rusefi/hw_microRusEfi/gerbers/0.4.8/placement_0.4.8.corrected.png

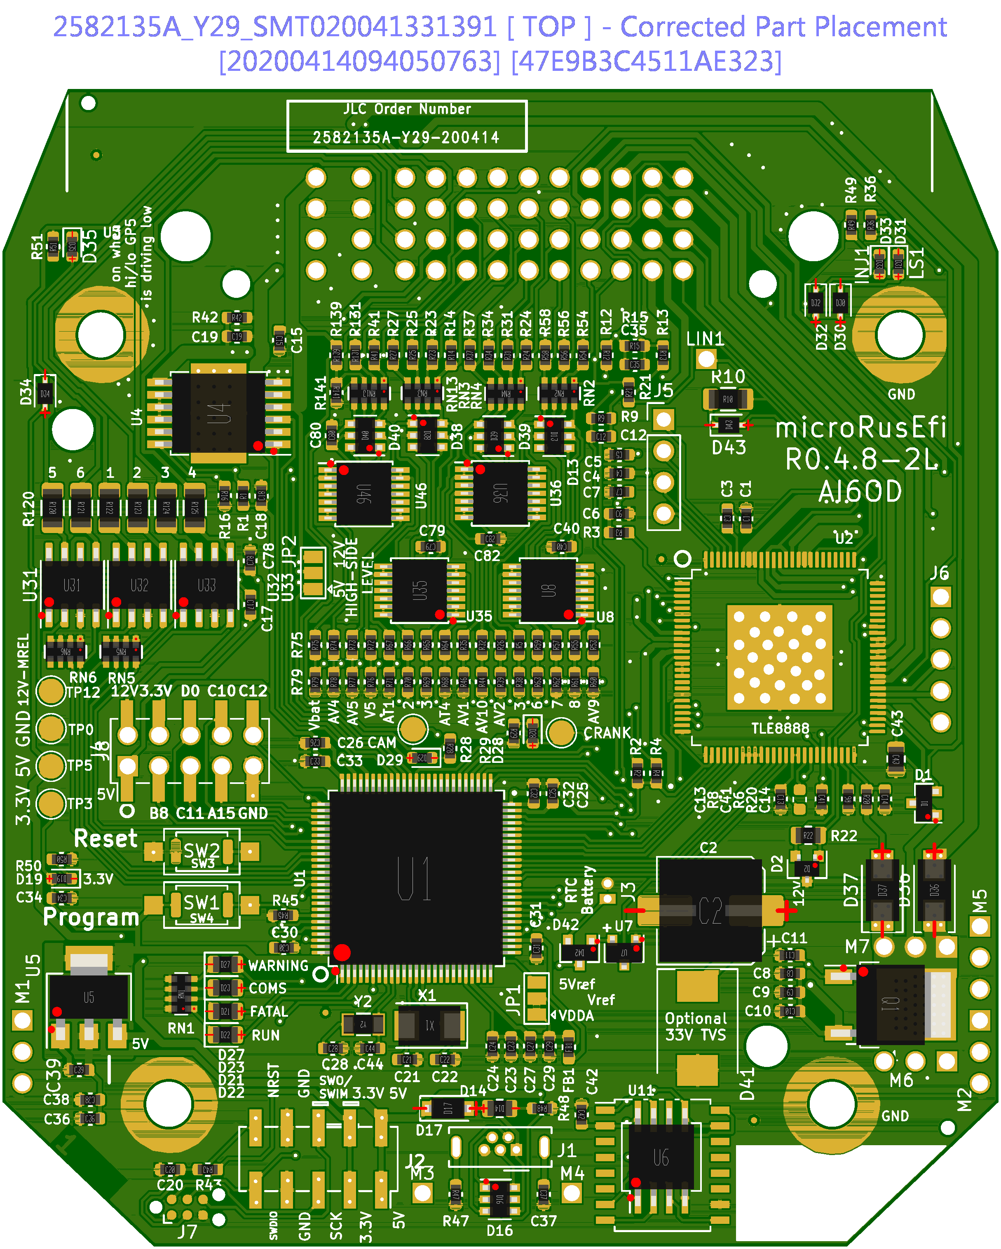
gerbers/0.4.8/placement_0.4.8.corrected.png
