rusefi/hw_microRusEfi/gerbers/0.4.8/placement_0.4.8.corrections.png

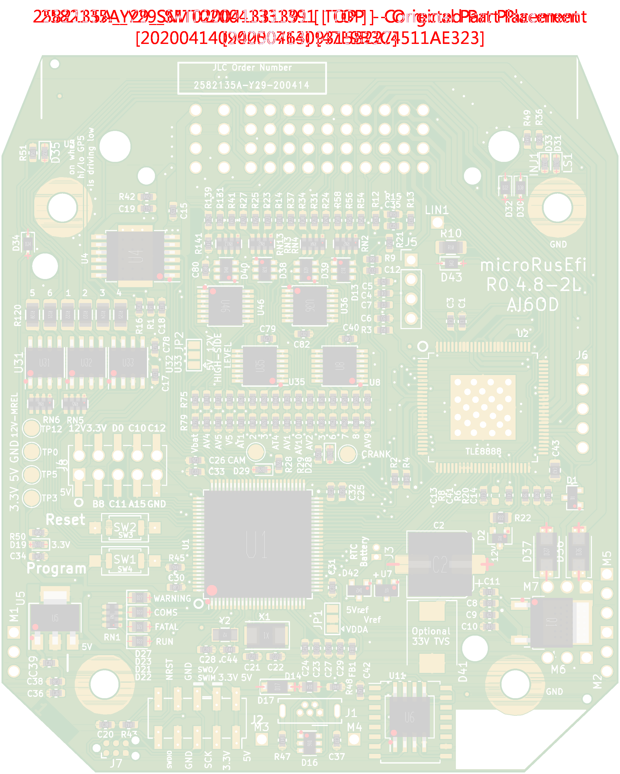
gerbers/0.4.8/placement_0.4.8.corrections.png
