rusefi/hw_microRusEfi/gerbers/0.5.0/placement_0.5.0.corrections.png

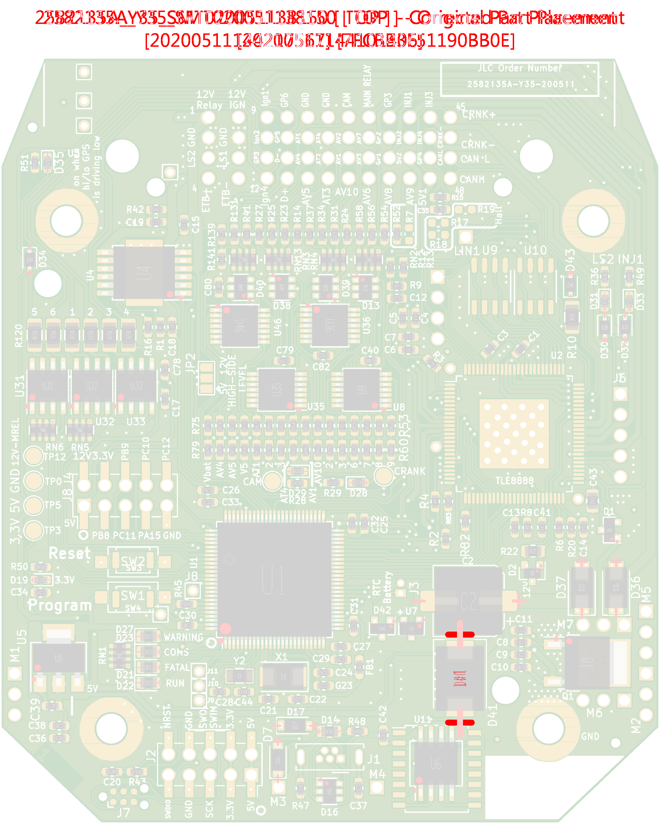
gerbers/0.5.0/placement_0.5.0.corrections.png
