rusefi/hw_microRusEfi/gerbers/R0.5.2/placement_0.5.2.corrected.png

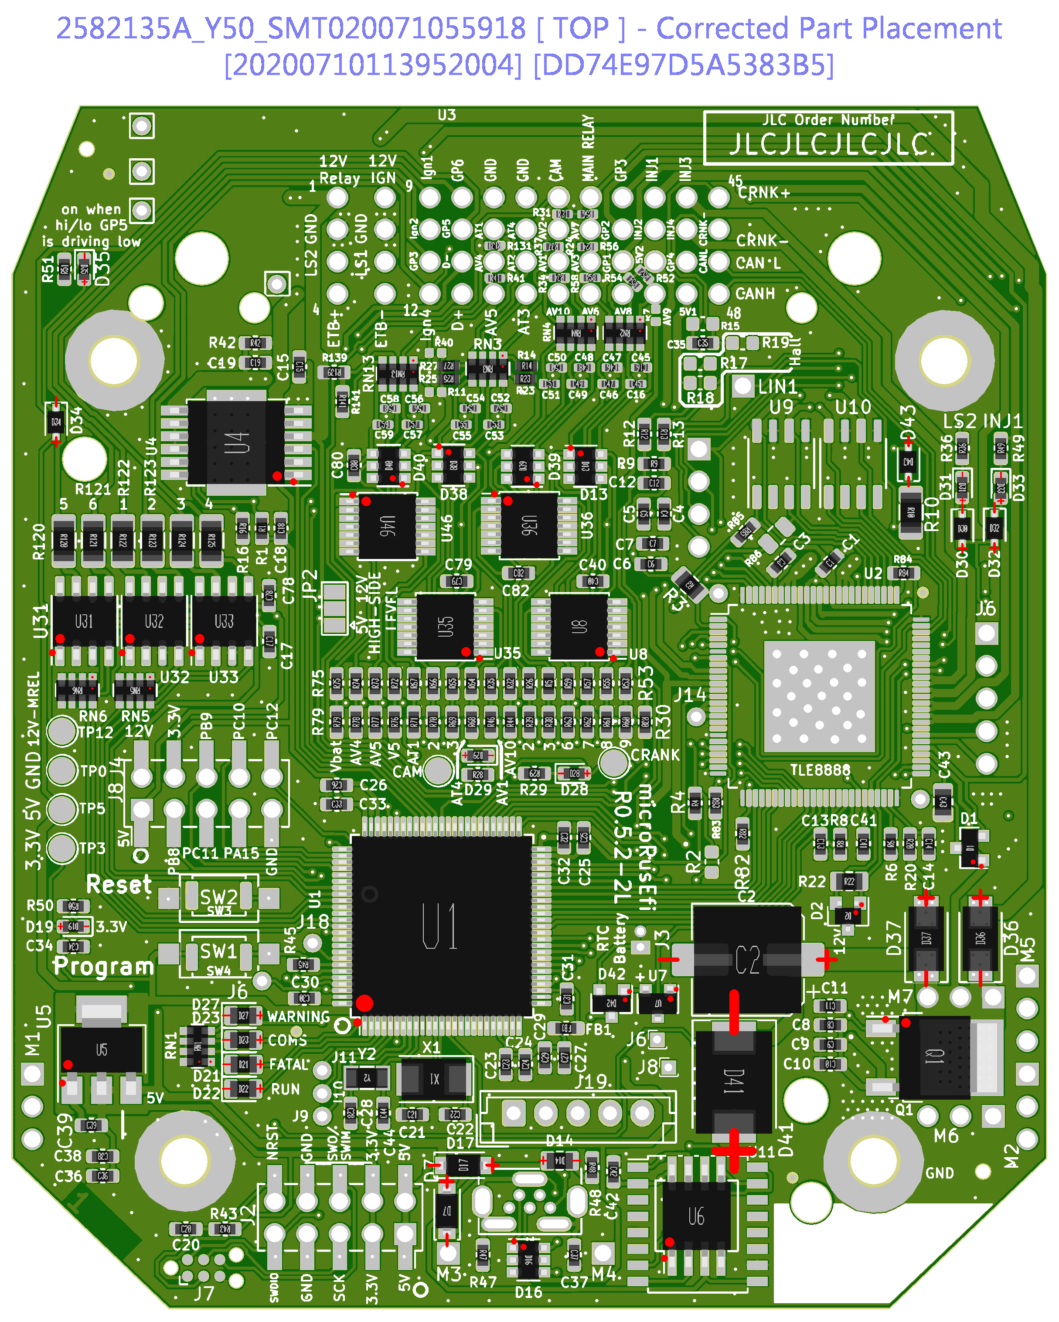
gerbers/R0.5.2/placement_0.5.2.corrected.png
