rusefi/hw_microRusEfi/gerbers/R0.6.0/92-Produce_DanZhi.SMT_Original_Snapshot.Bottom.2582135A_Y484.SMT024101961142.png

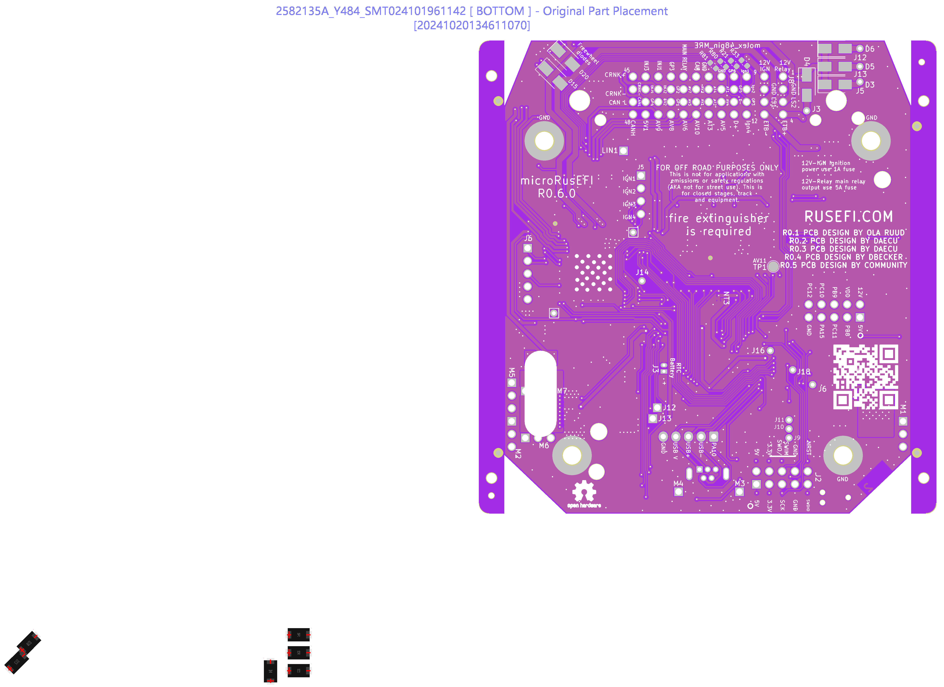
gerbers/R0.6.0/92-Produce_DanZhi.SMT_Original_Snapshot.Bottom.2582135A_Y484.SMT024101961142.png
