rusefi/hw_microRusEfi/gerbers/R0.6.0/31968-Produce_DanZhi.SMT_Original_Snapshot.Top.2582135A_Y484.SMT024101961142.png

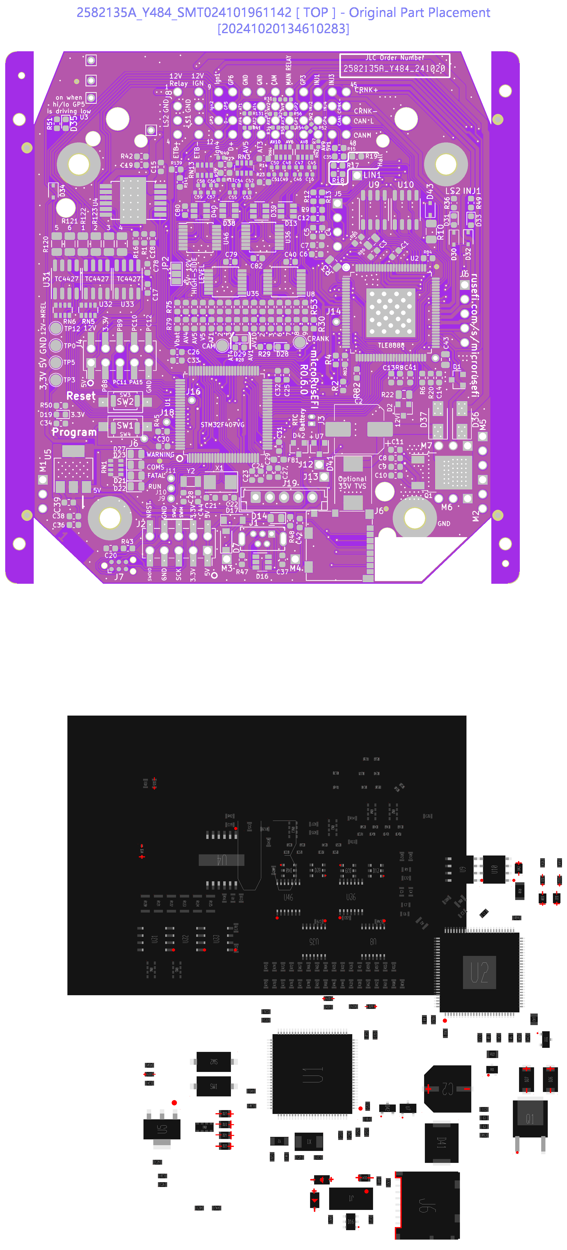
gerbers/R0.6.0/31968-Produce_DanZhi.SMT_Original_Snapshot.Top.2582135A_Y484.SMT024101961142.png
