rusefi/hw_microRusEfi/gerbers/R0.6.0/44555794432-Produce_DanZhi.SMT_Snapshot.Bottom.2582135A_Y484.SMT024101961142.png

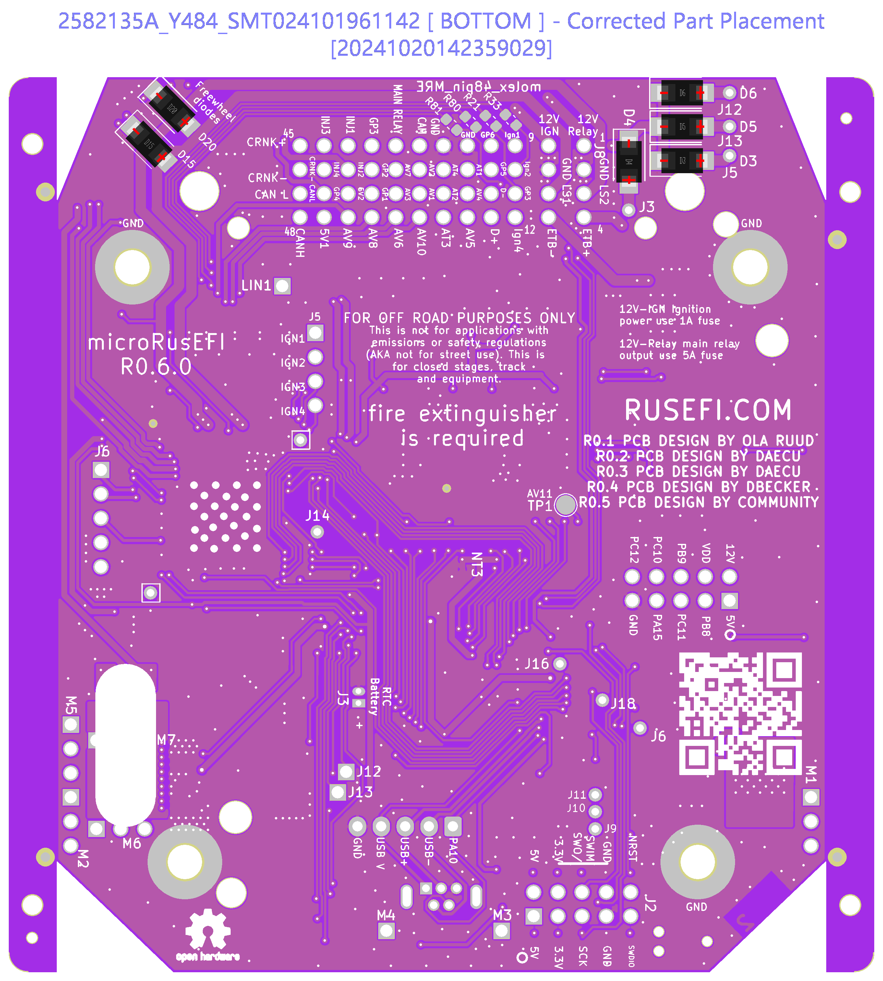
gerbers/R0.6.0/44555794432-Produce_DanZhi.SMT_Snapshot.Bottom.2582135A_Y484.SMT024101961142.png
