rusefi/hw_microRusEfi/gerbers/R0.6.0/27541634936832-Produce_DanZhi.SMT_Snapshot.Top.2582135A_Y484.SMT024101961142.png

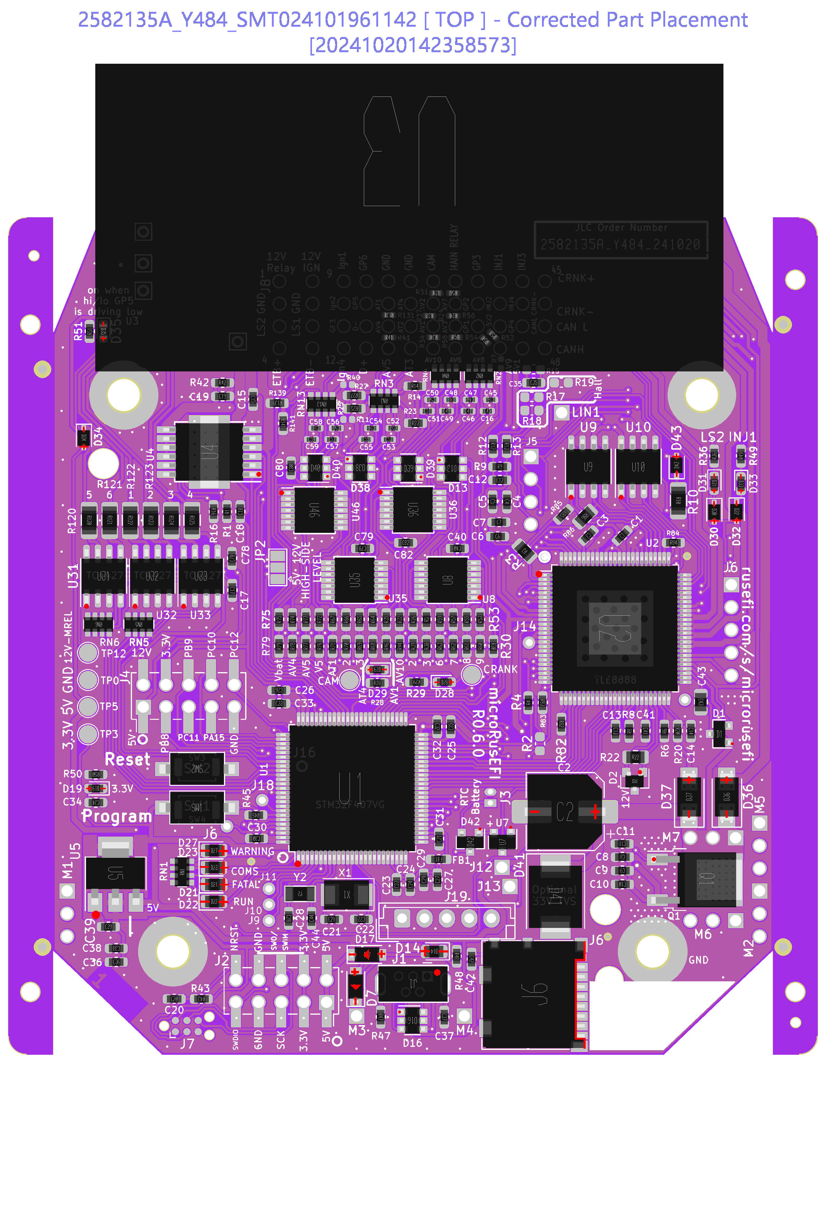
gerbers/R0.6.0/27541634936832-Produce_DanZhi.SMT_Snapshot.Top.2582135A_Y484.SMT024101961142.png
