rusefi/hw_microRusEfi/gerbers/R0.6.0/Produce_DanZhi.SMT_Original_Snapshot.Top.2582135A_Y214.SMT0220411715433.png

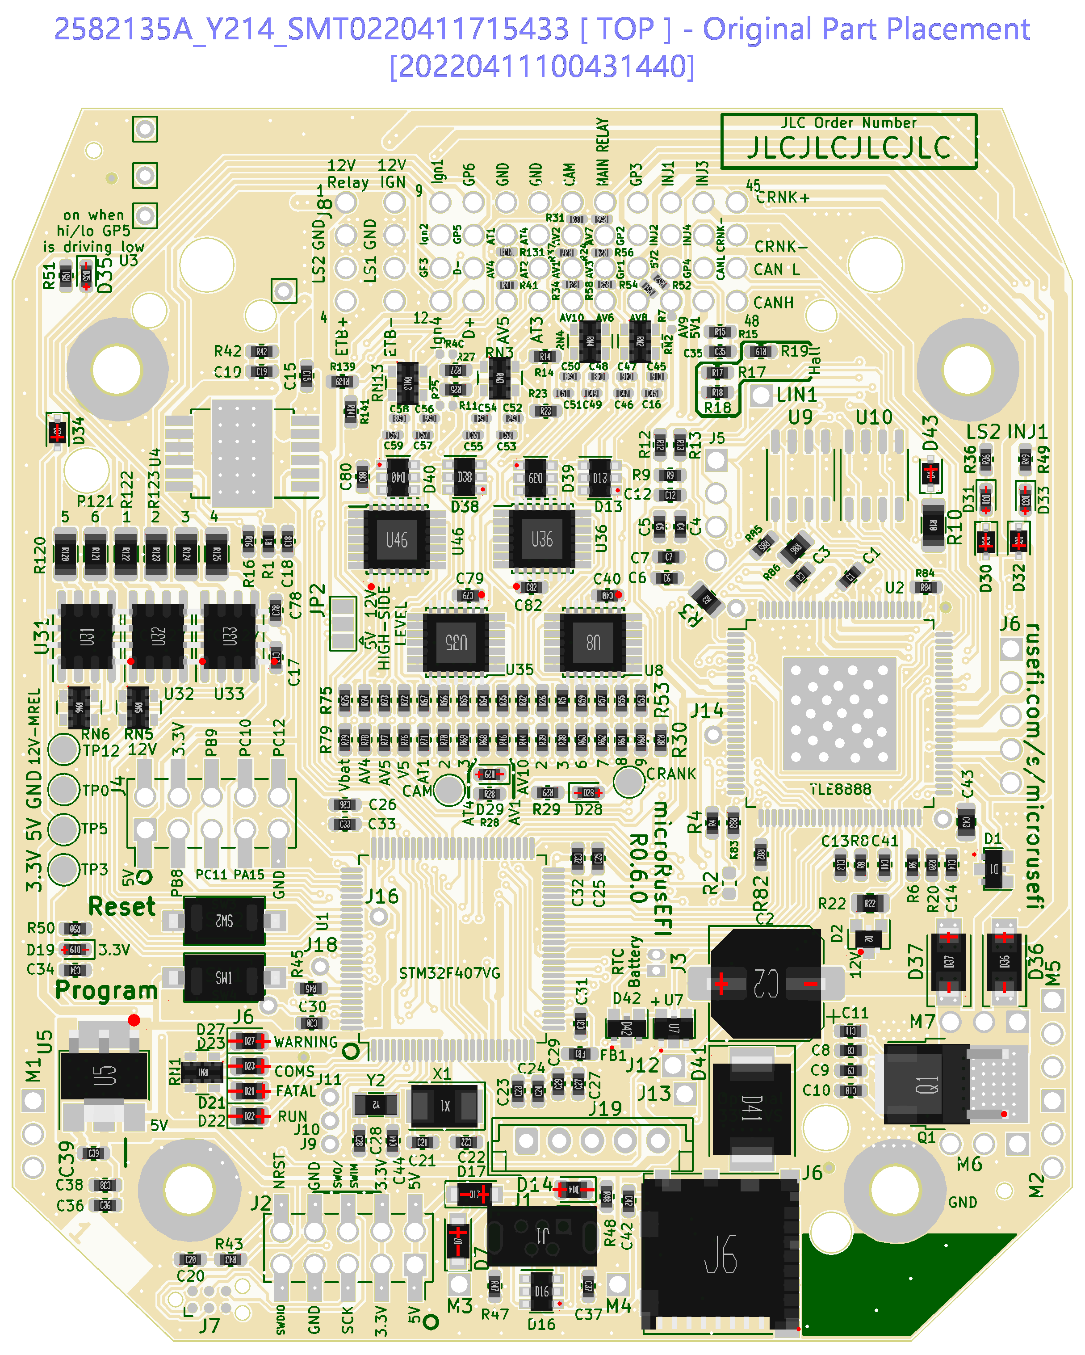
gerbers/R0.6.0/Produce_DanZhi.SMT_Original_Snapshot.Top.2582135A_Y214.SMT0220411715433.png
