rusefi/hw_microRusEfi/gerbers/R0.6.0/Produce_DanZhi.SMT_Snapshot.Top.2582135A_Y332.SMT02307111312351.png

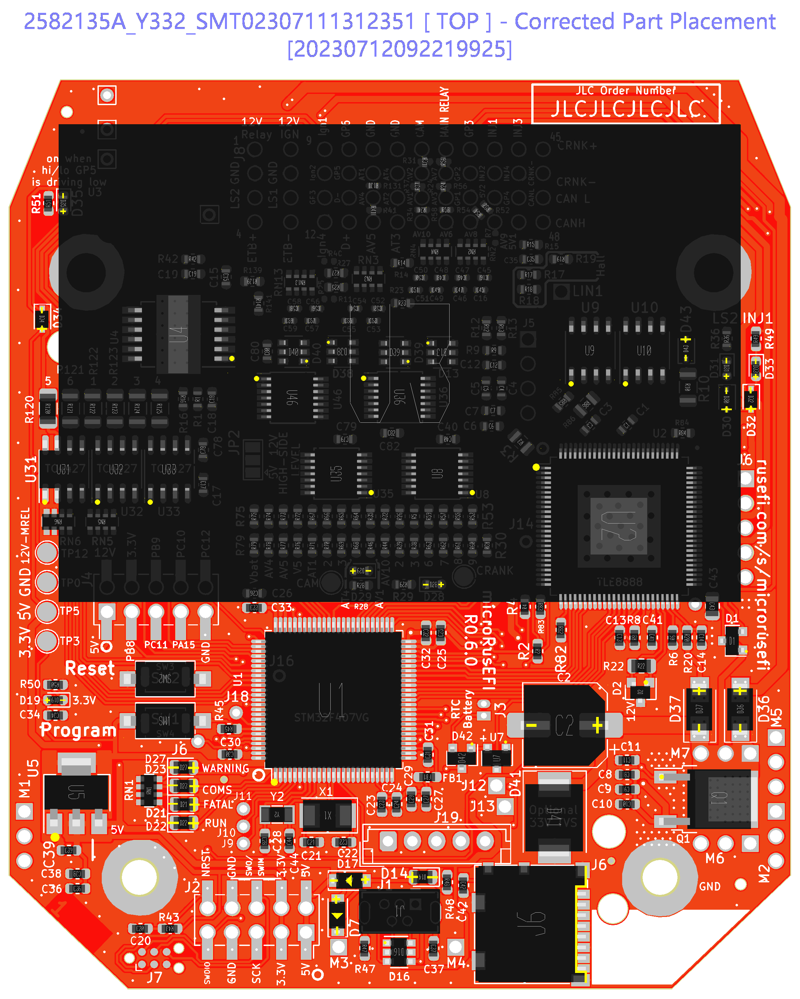
gerbers/R0.6.0/Produce_DanZhi.SMT_Snapshot.Top.2582135A_Y332.SMT02307111312351.png
