rusefi/hw_microRusEfi/gerbers/R0.6.0/micro_rusEFI.pdf

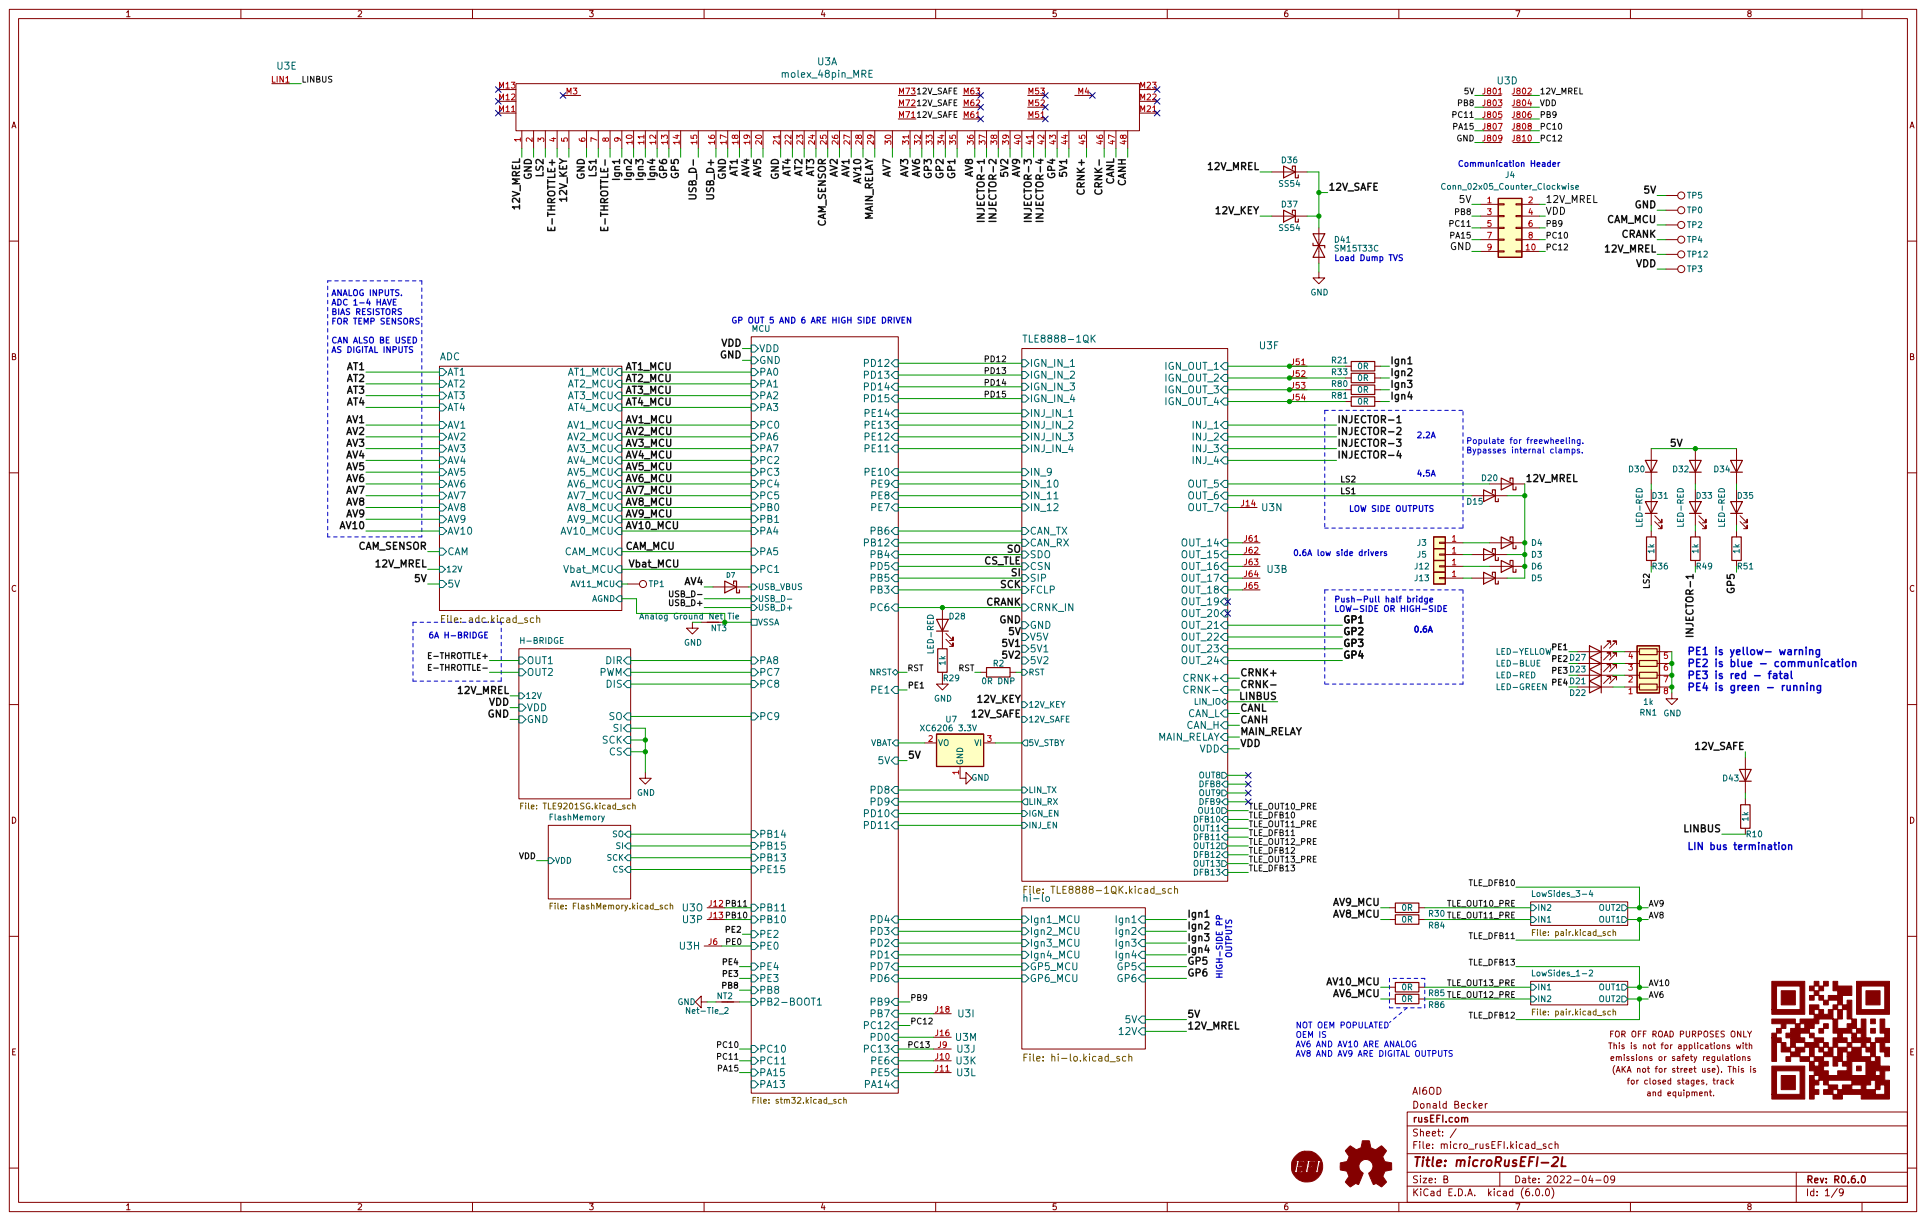
[picture p56: page 1]

Push-Pull half bridge LOW-SIDE OR HIGH-SIDE GP OUT 5 AND 6 ARE HIGH SIDE DRIVEN

NOT OEM POPULATED OEM IS AV6 AND AV10 ARE ANALOG

for closed stages, track FOR OFF ROAD PURPOSES ONLY
This is not for applications with
emissions or safety regulations
(AKA not for street use). This is

AV8 AND AV9 ARE DIGITAL OUTPUTS

File: micro_rusEFI.kicad_sch Sheet: / rusEFI.com

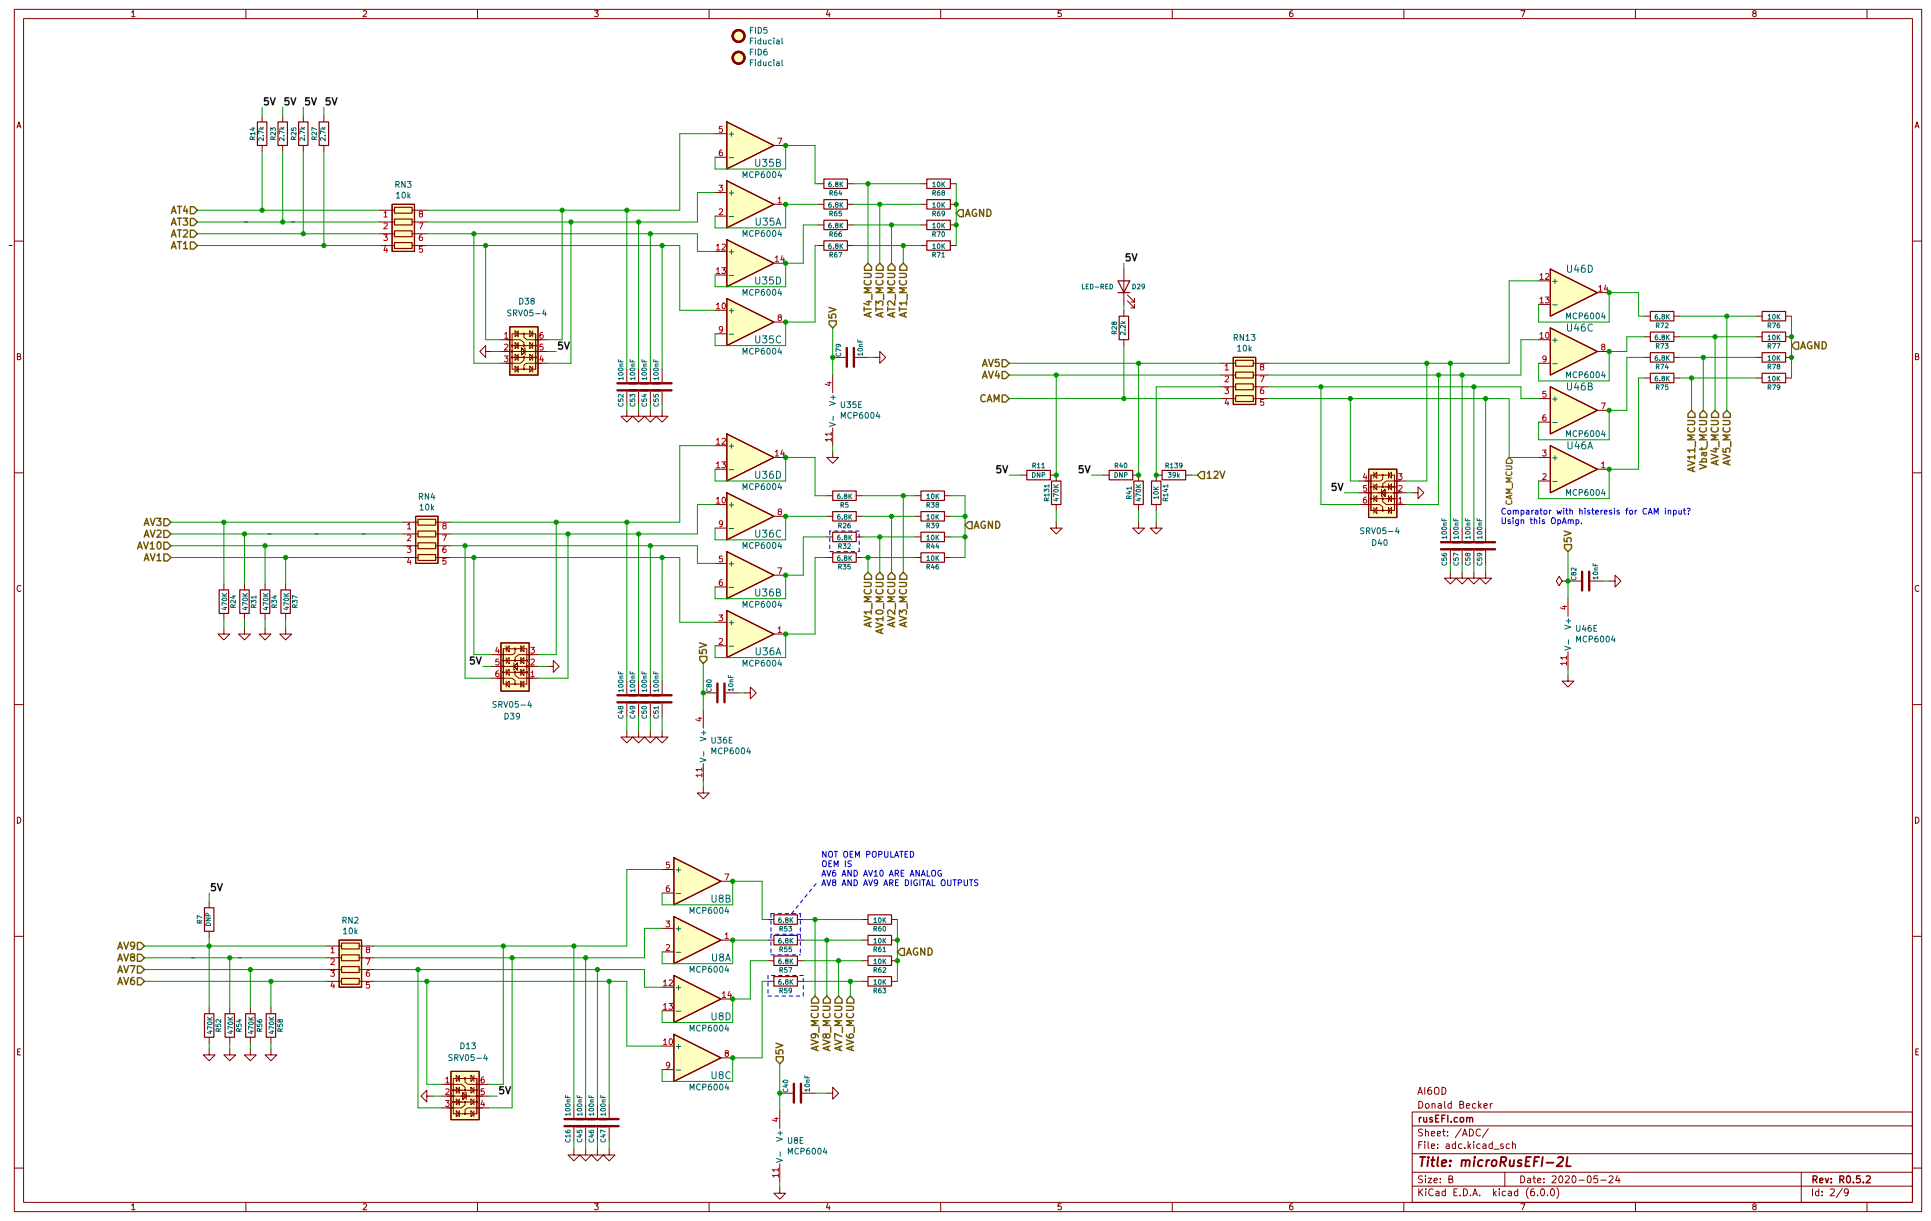
[picture p57: page 2]

Usign this OpAmp. NOT OEM POPULATED OEM IS AV6 AND AV10 ARE ANALOG

Comparator with histeresis for CAM input?

AV8 AND AV9 ARE DIGITAL OUTPUTS

File: adc.kicad_sch Sheet: /ADC/ rusEFI.com

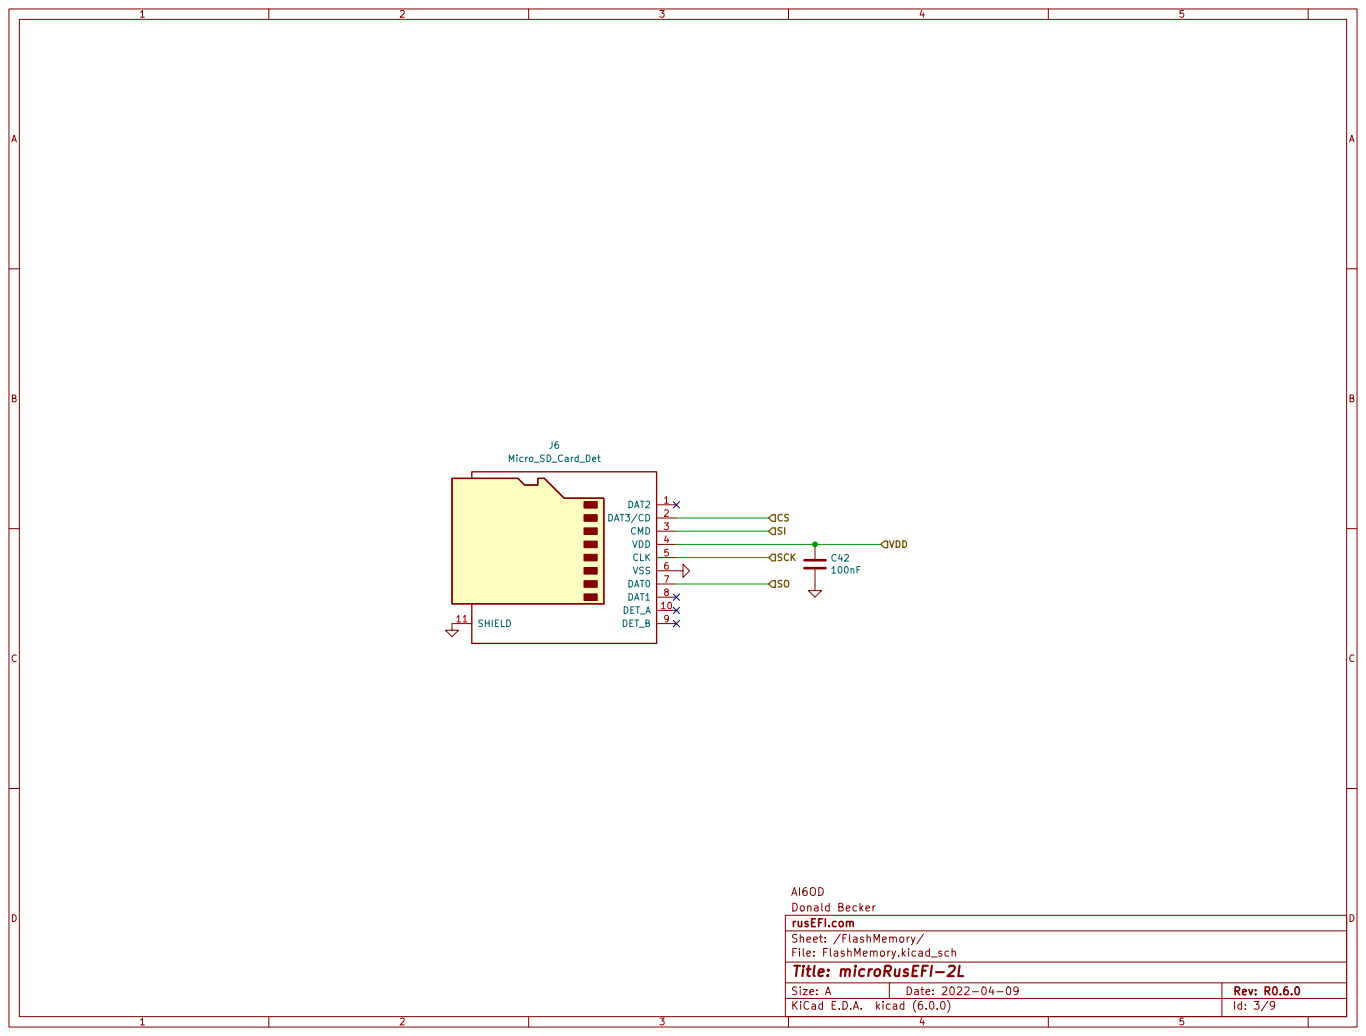
[picture p58: page 3]

Sheet: /FlashMemory/ rusEFI.com

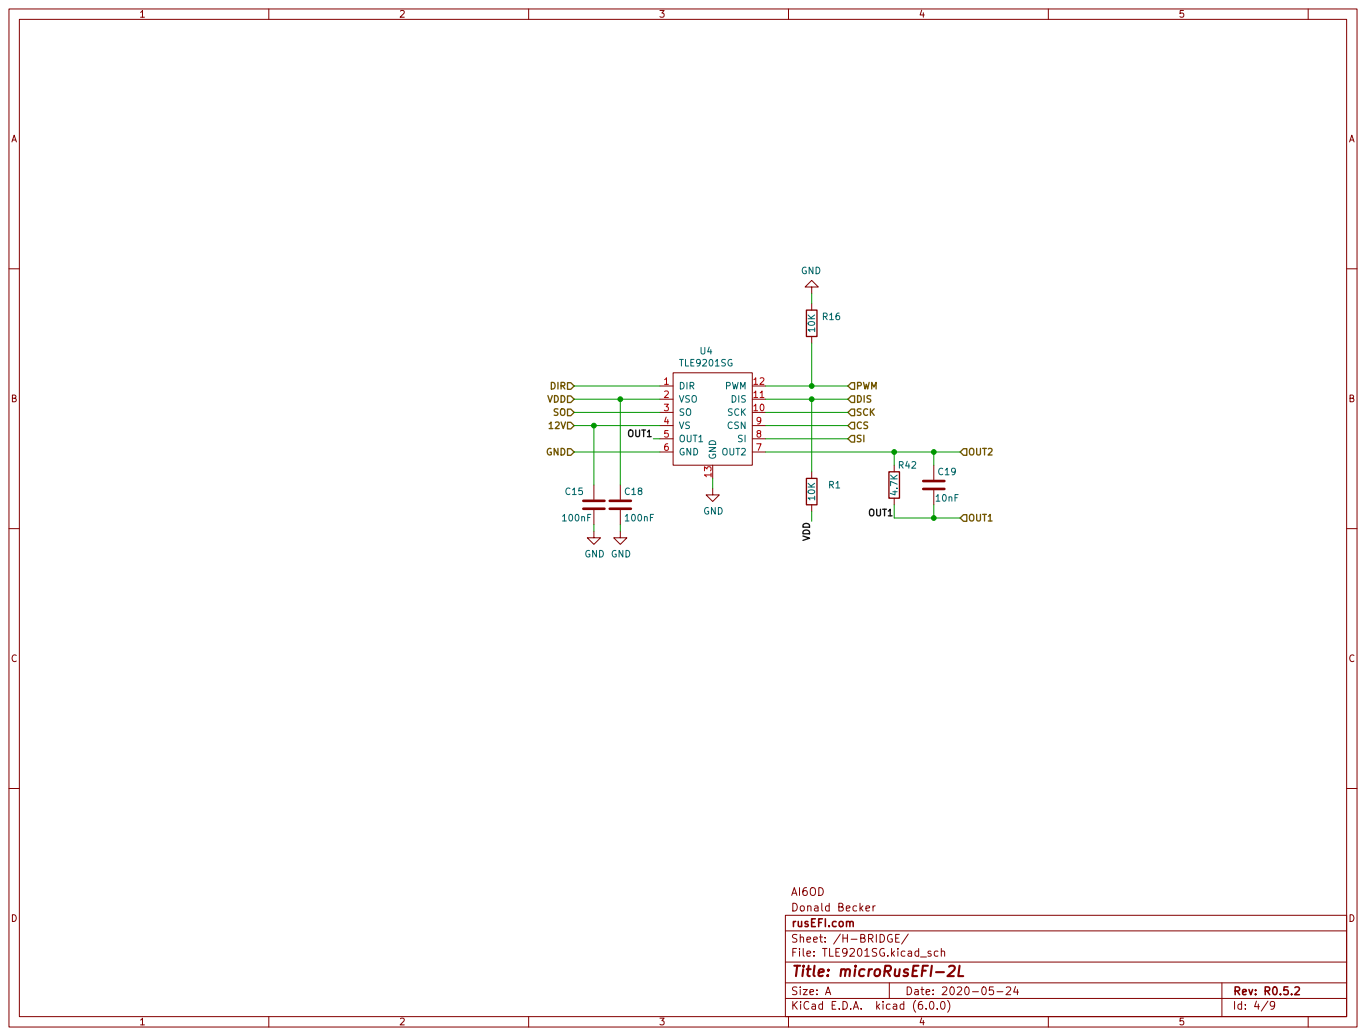
[picture p59: page 4]

File: TLE9201SG.kicad_sch Sheet: /H-BRIDGE/ rusEFI.com

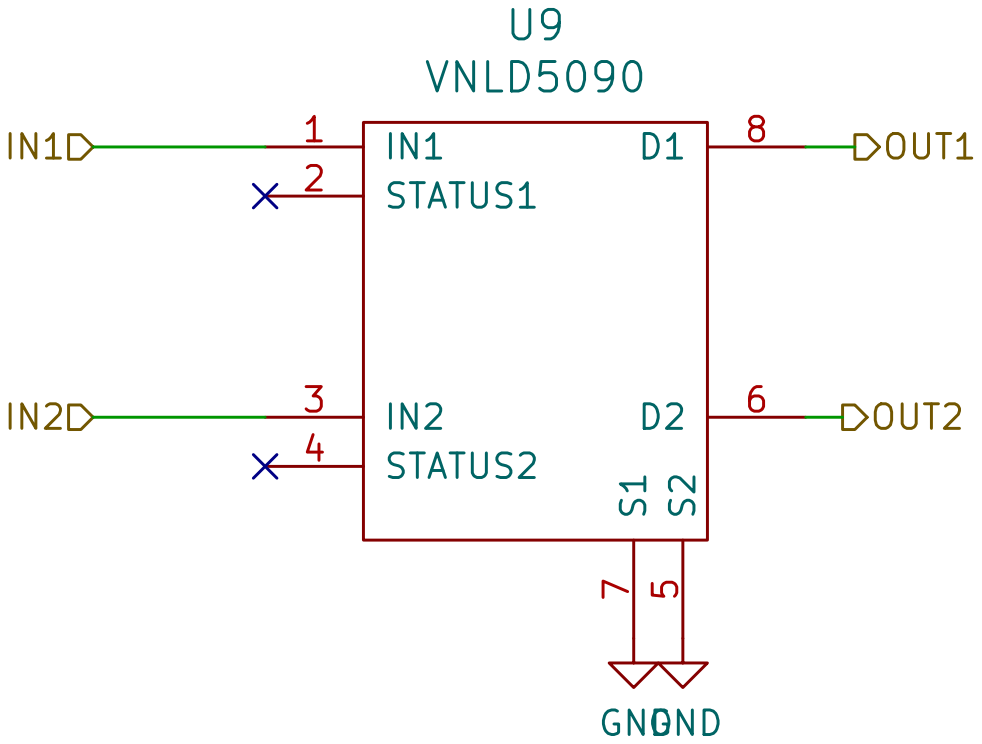
[picture p60: page 5]

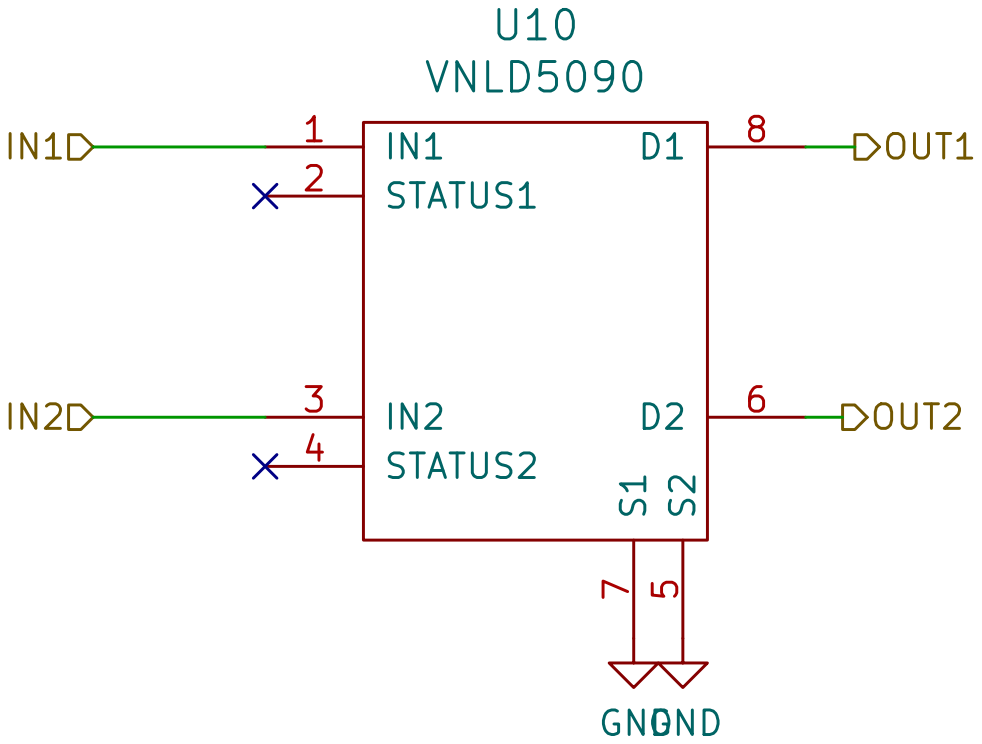
[picture p61: page 6]

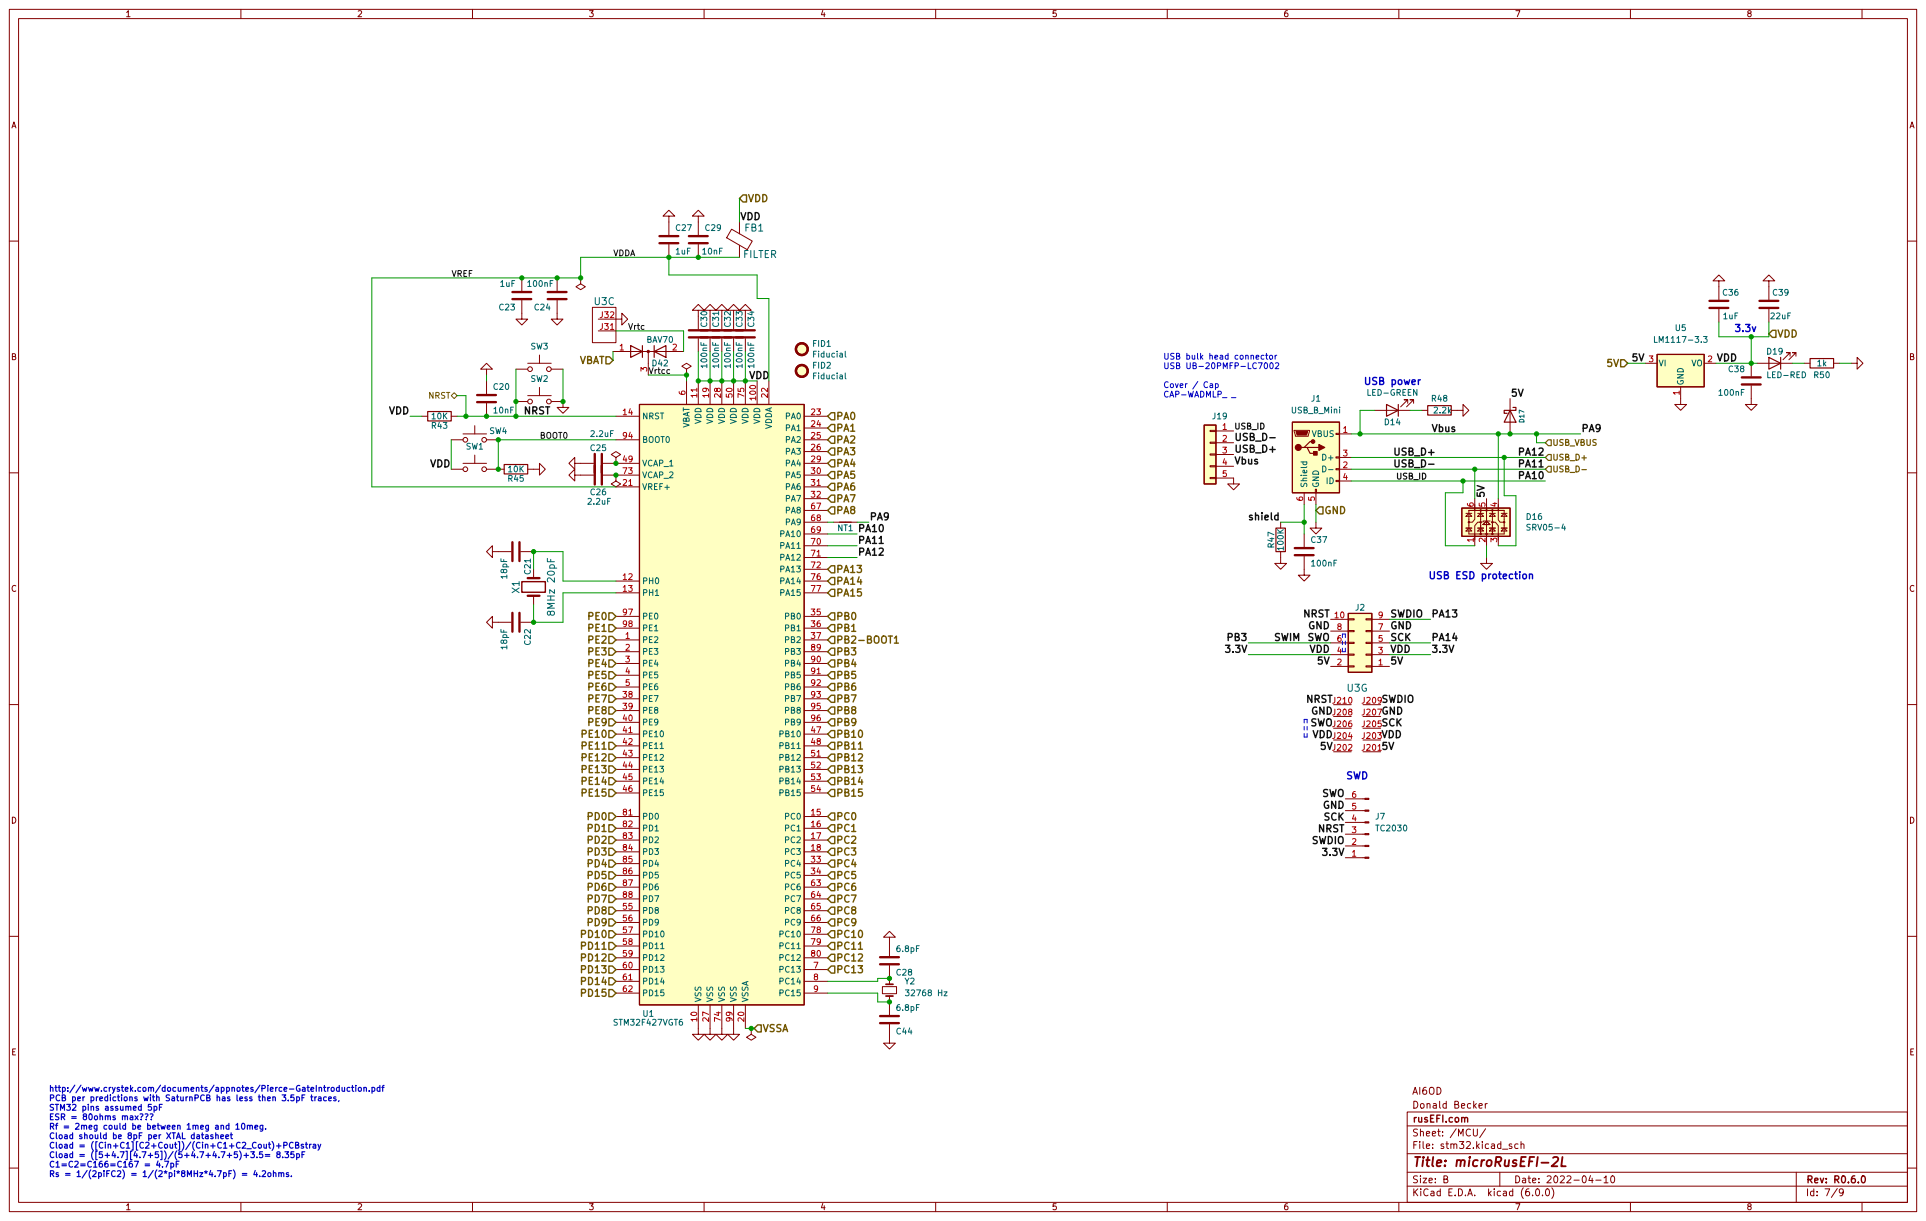
[picture p62: page 7]

3.3v USB power USB bulk head connector USB UB-20PMFP-LC7002 Cover / Cap CAP-WADMLP_ _

http://www.crystek.com/documents/appnotes/Pierce-GateIntroduction.pdf
PCB per predictions with SaturnPCB has less then 3.5pF traces,
STM32 pins assumed 5pF ESR = 80ohms max??? Rf = 2meg could be between 1meg and 10meg.

File: stm32.kicad_sch Sheet: /MCU/ rusEFI.com

Cload should be 8pF per XTAL datasheet
Cload = ([Cin+C1][C2+Cout])/(Cin+C1+C2_Cout)+PCBstray
Cload = ([5+4.7][4.7+5])/(5+4.7+4.7+5)+3.5= 8.35pF
Rs = 1/(2piFC2) = 1/(2*pi*8MHz*4.7pF) = 4.2ohms.

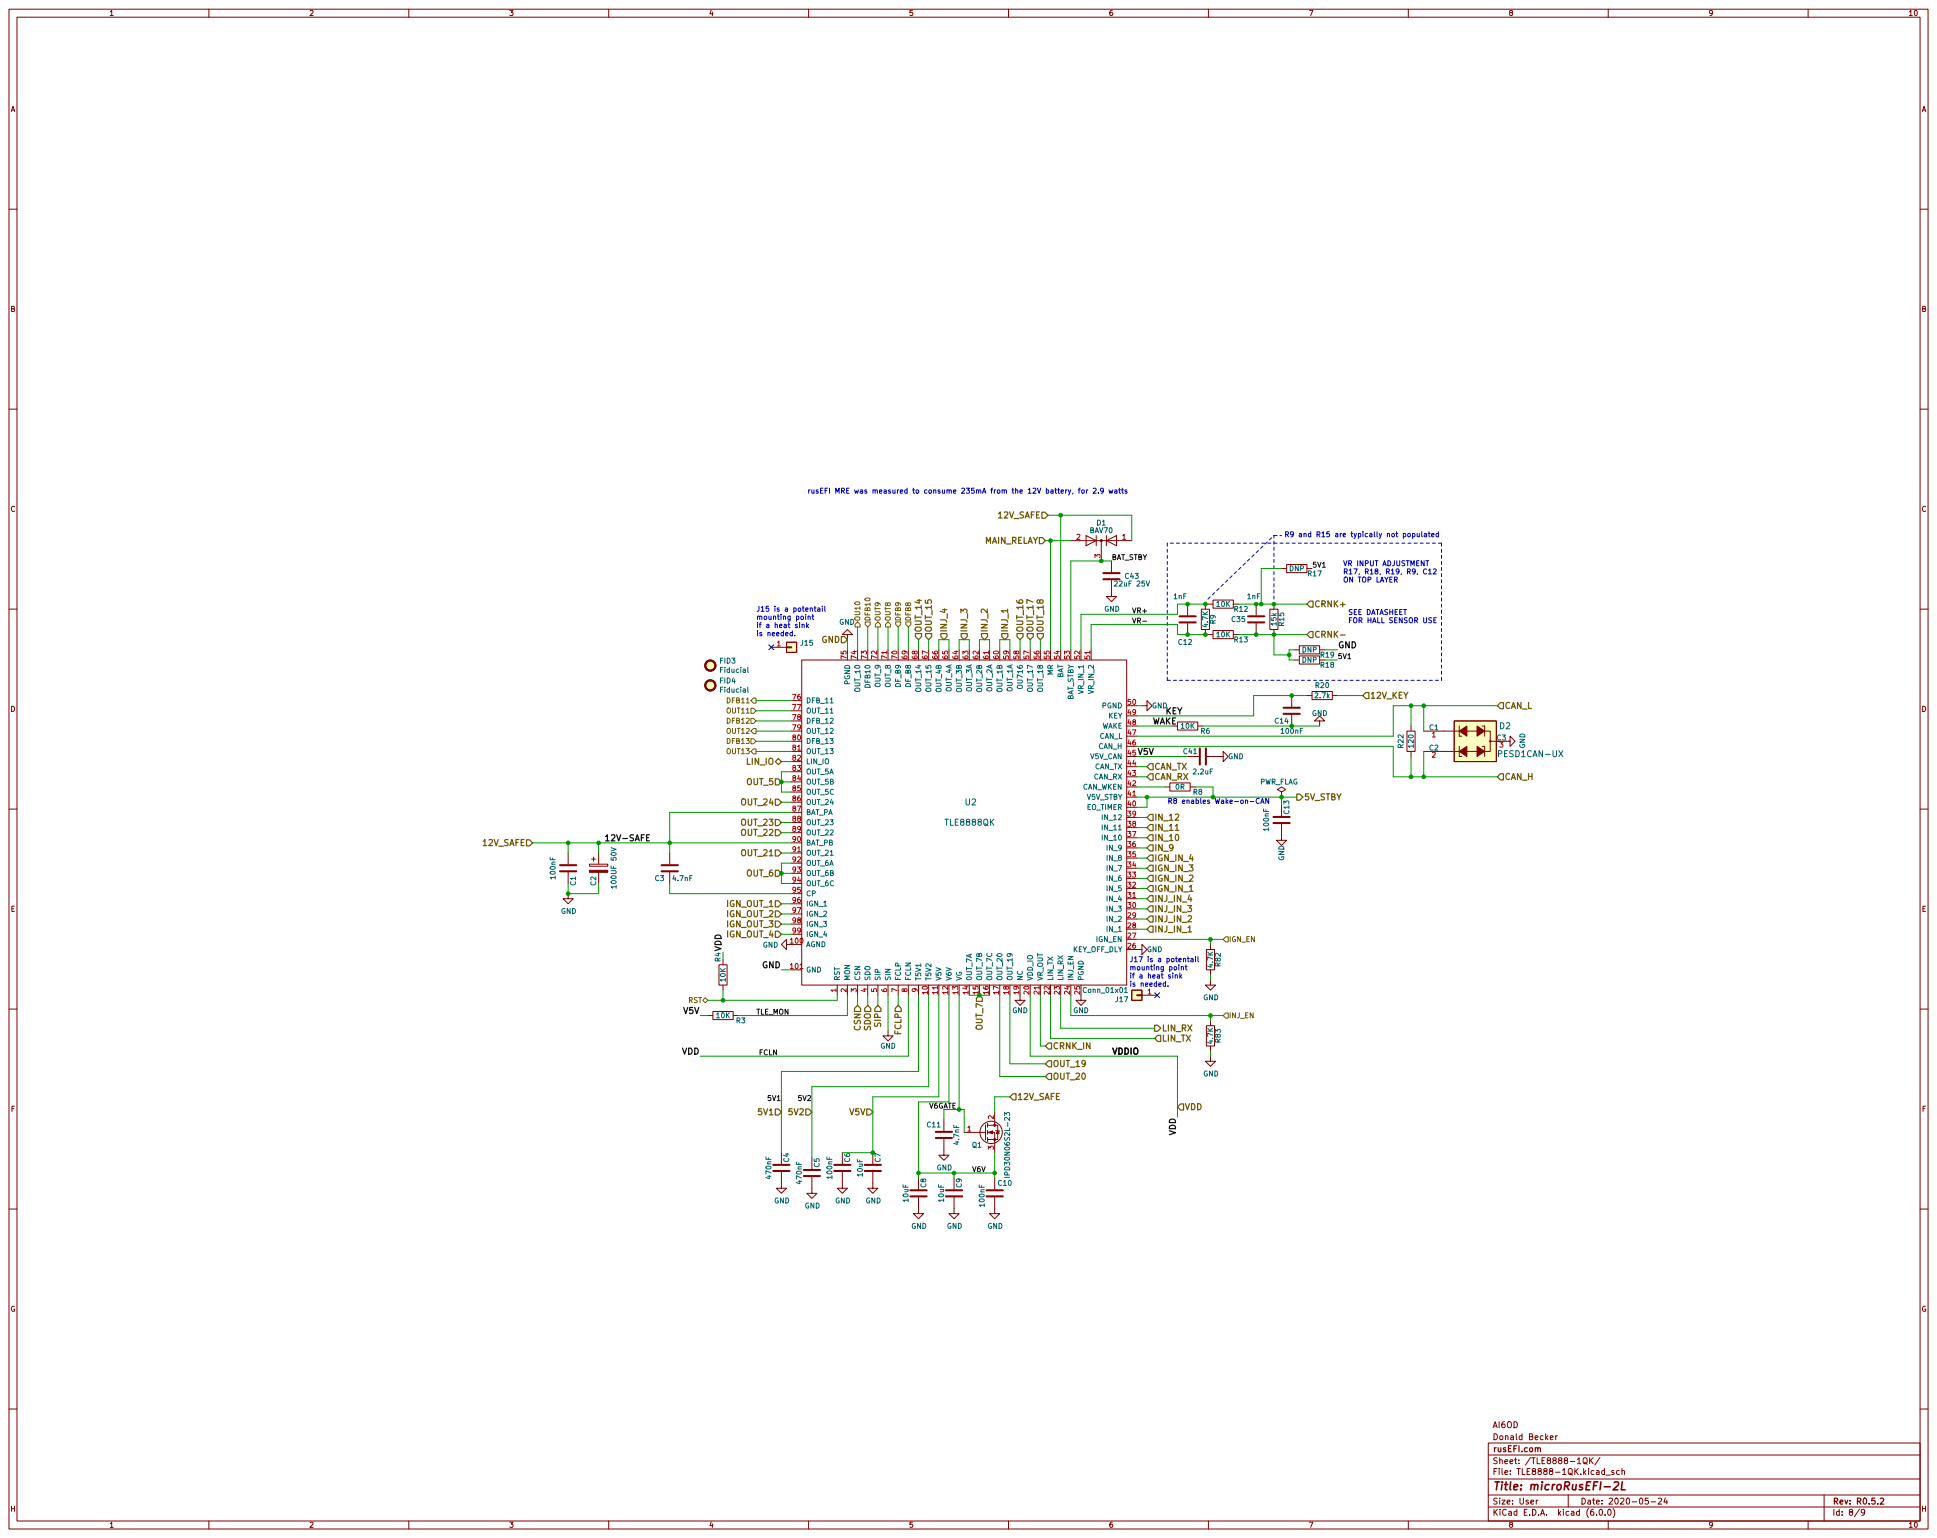
[picture p63: page 8]

R9 and R15 are typically not populated

VR INPUT ADJUSTMENT R17, R18, R19, R9, C12 ON TOP LAYER

5 PGND 50 VR_IN_2 51 VR_IN_1 52 BAT_STBY 53 BAT 54 MR 55 OUT_18 56 OUT_17 57 OU716 58 OUT_1A 59 SIN

1 T5V2 10 AGND 100 GND 101 V5V 11 V6V 12 VG 13 0UT_7A 14 OUT_7B 15 OUT_7C 16 OUT_20 17 OUT_19 18 NC 19 MON

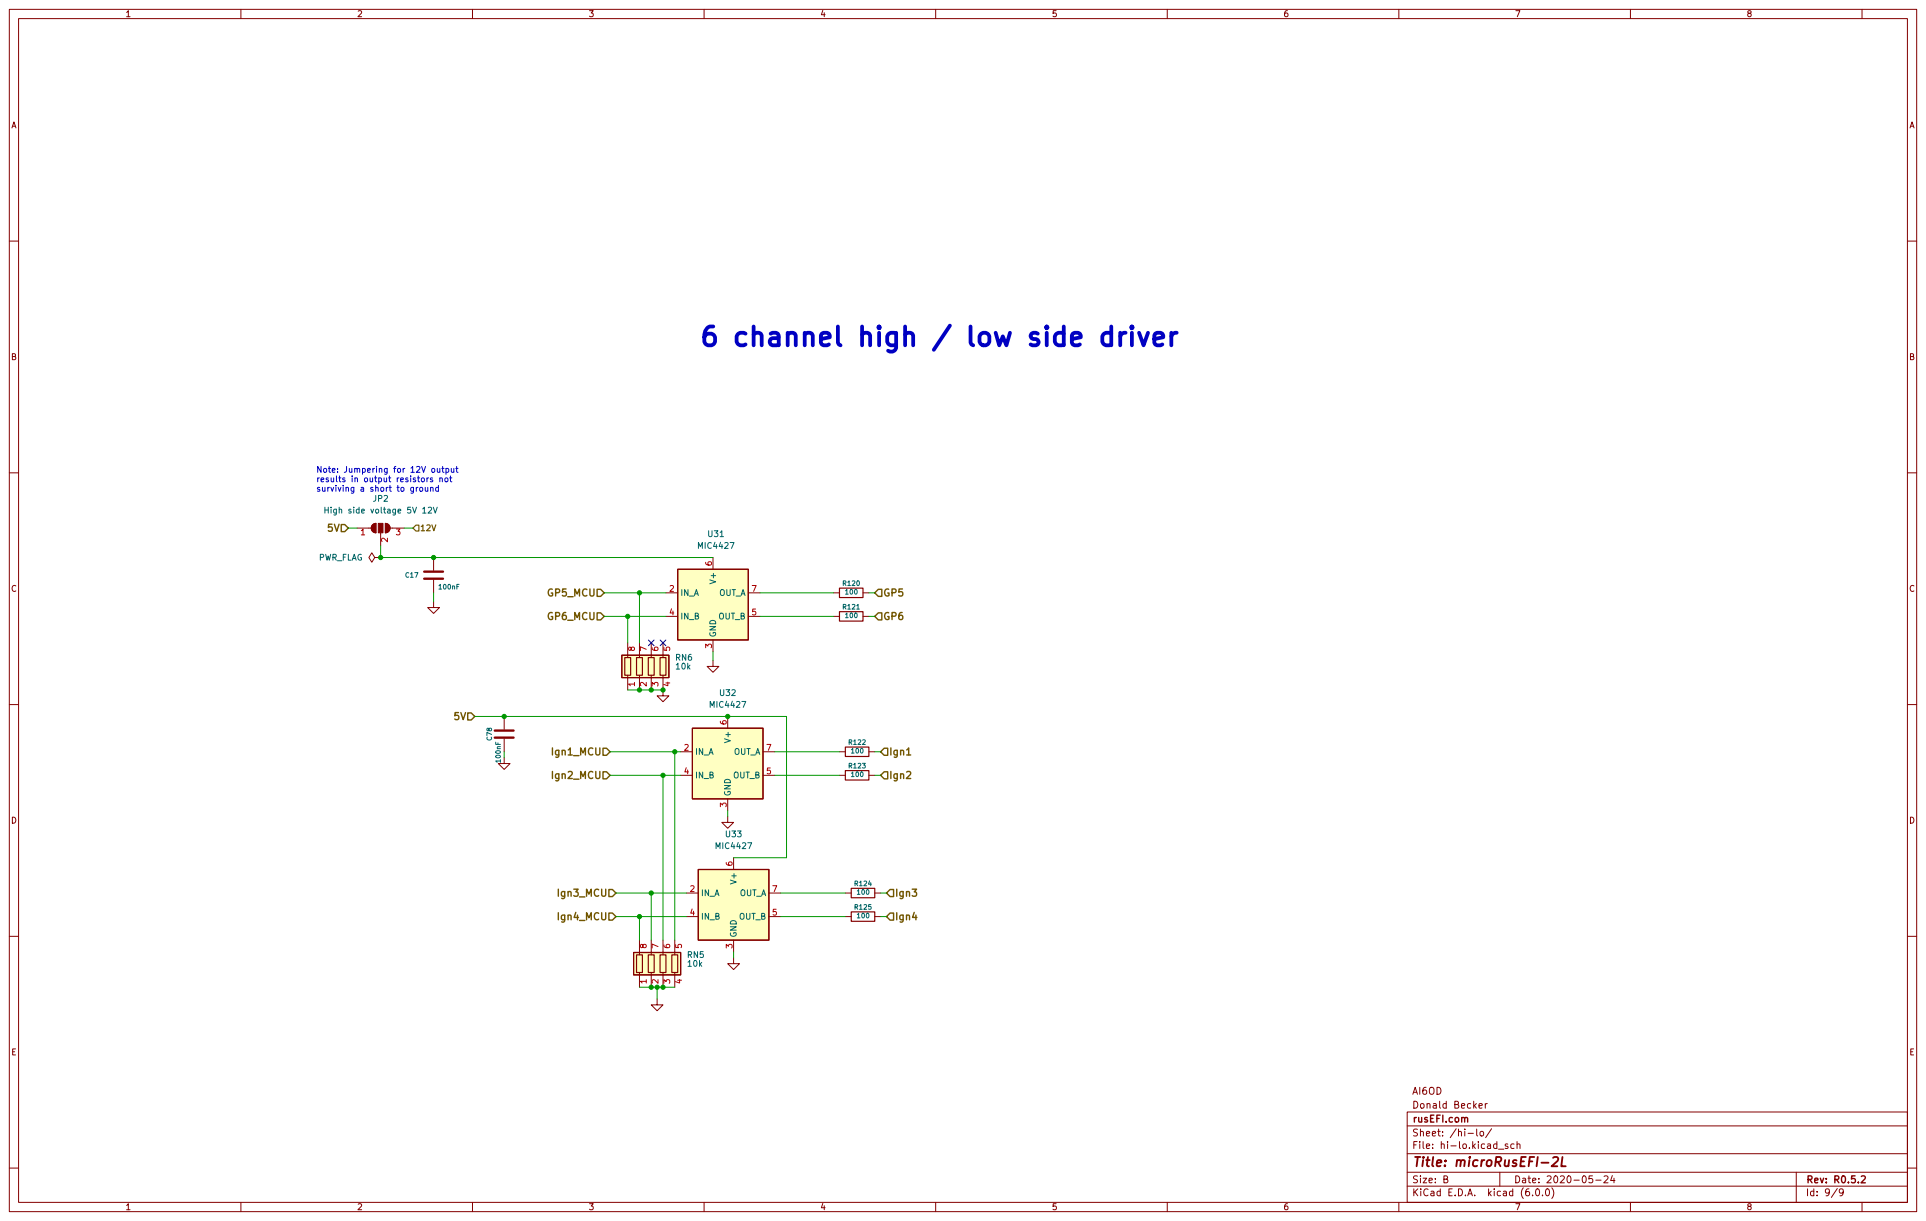
[picture p64: page 9]

6 channel high / low side driver

12V Note: Jumpering for 12V output
results in output resistors not
surviving a short to ground

File: hi-lo.kicad_sch Sheet: /hi-lo/ rusEFI.com
