rusefi/hw_microRusEfi/zMRETestFixture_PCB_layout.pdf

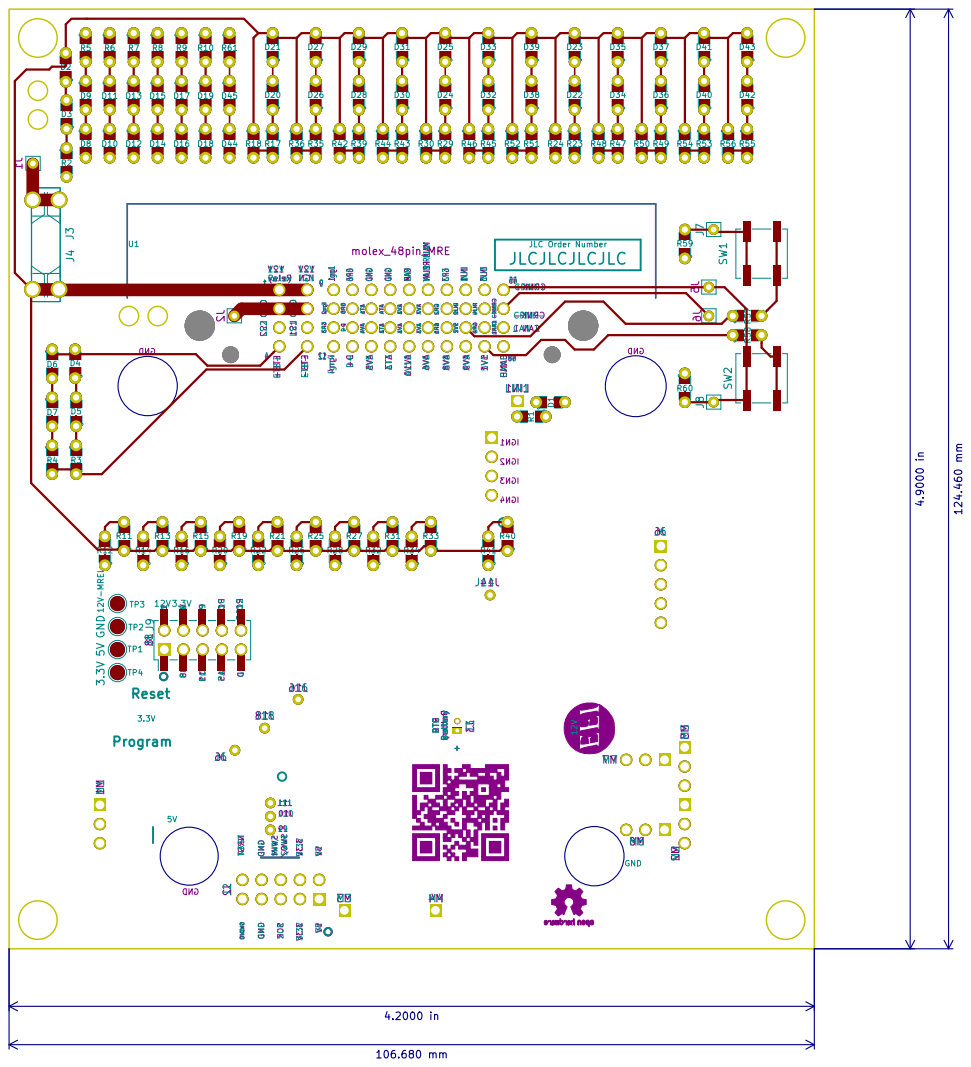
[picture p79: page 1]
