rusefi/hw_microRusEfi/micro_rusEFI_PCB.pdf

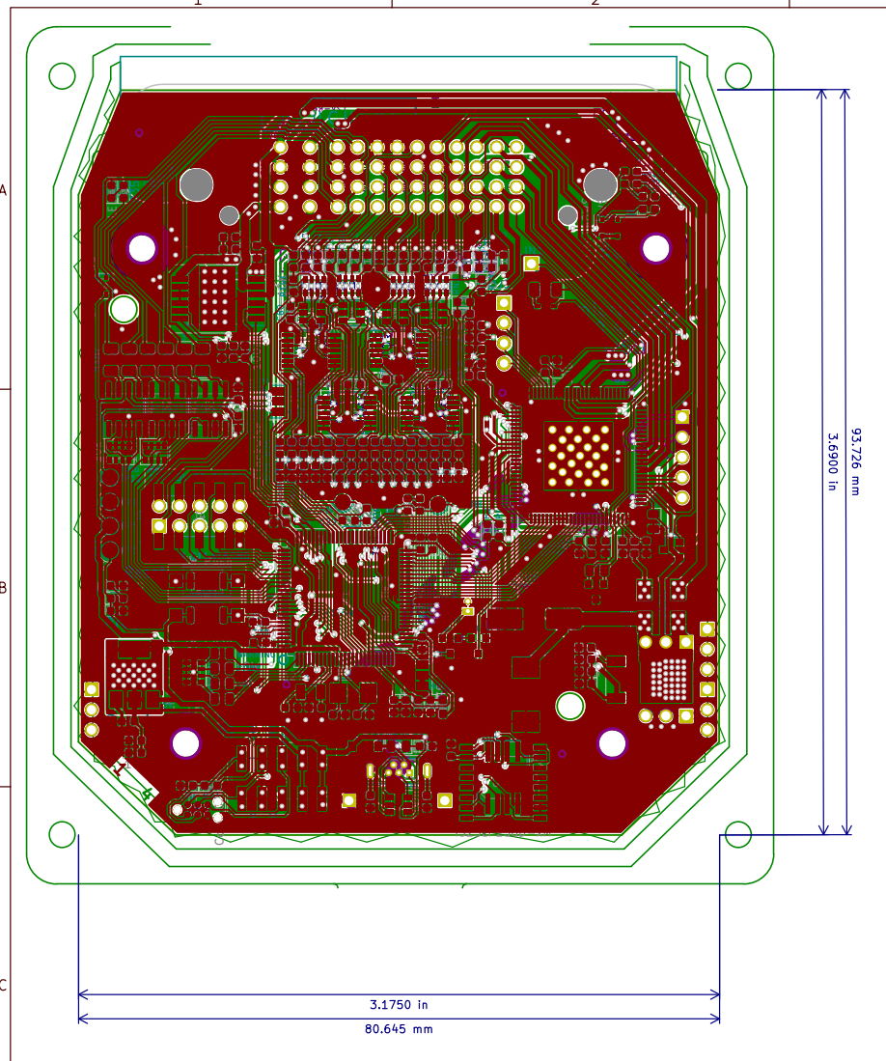
[picture p80: page 1]
