rusefi/hw_microRusEfi/CKKB48-1-A.pdf

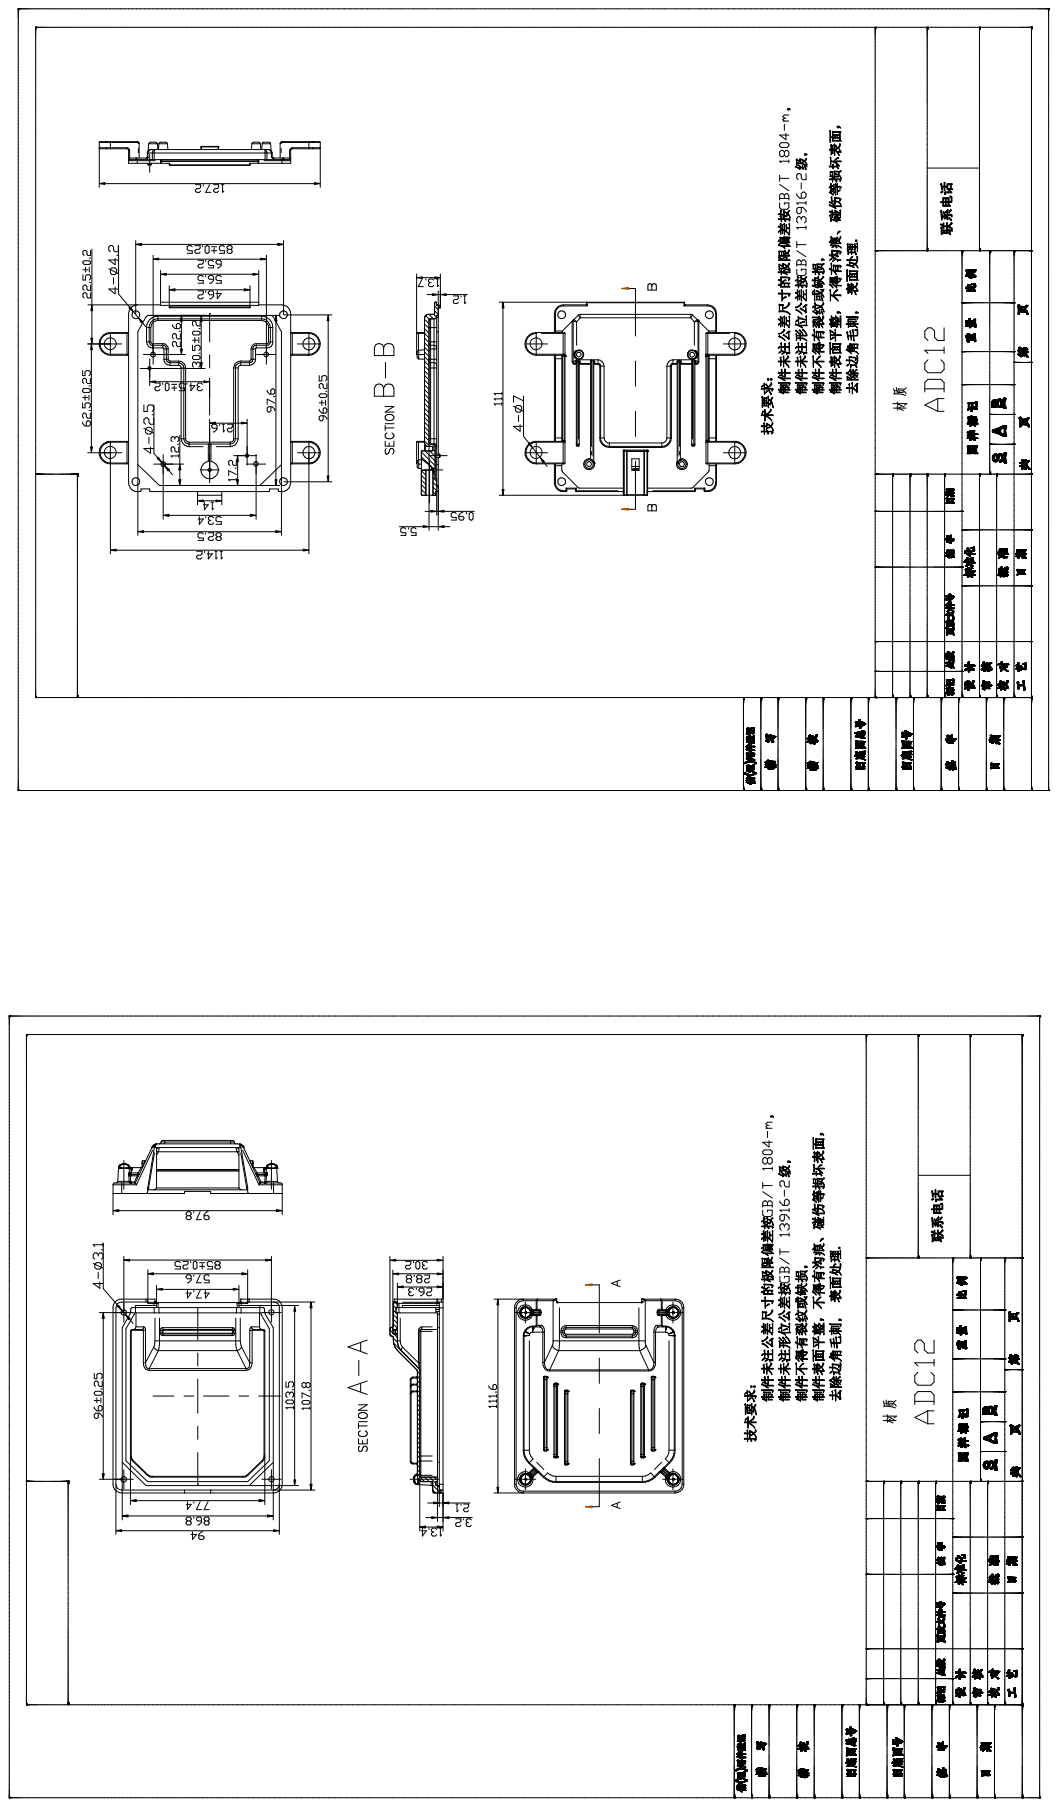
[picture p81: page 1]
